AfonsoLopo/migrane-kbd/pcbs/rev3.0/MasterLed.kicad_sch

## KiCad design pcbs/rev3.0/MasterLed.kicad_sch (2025-11-08)

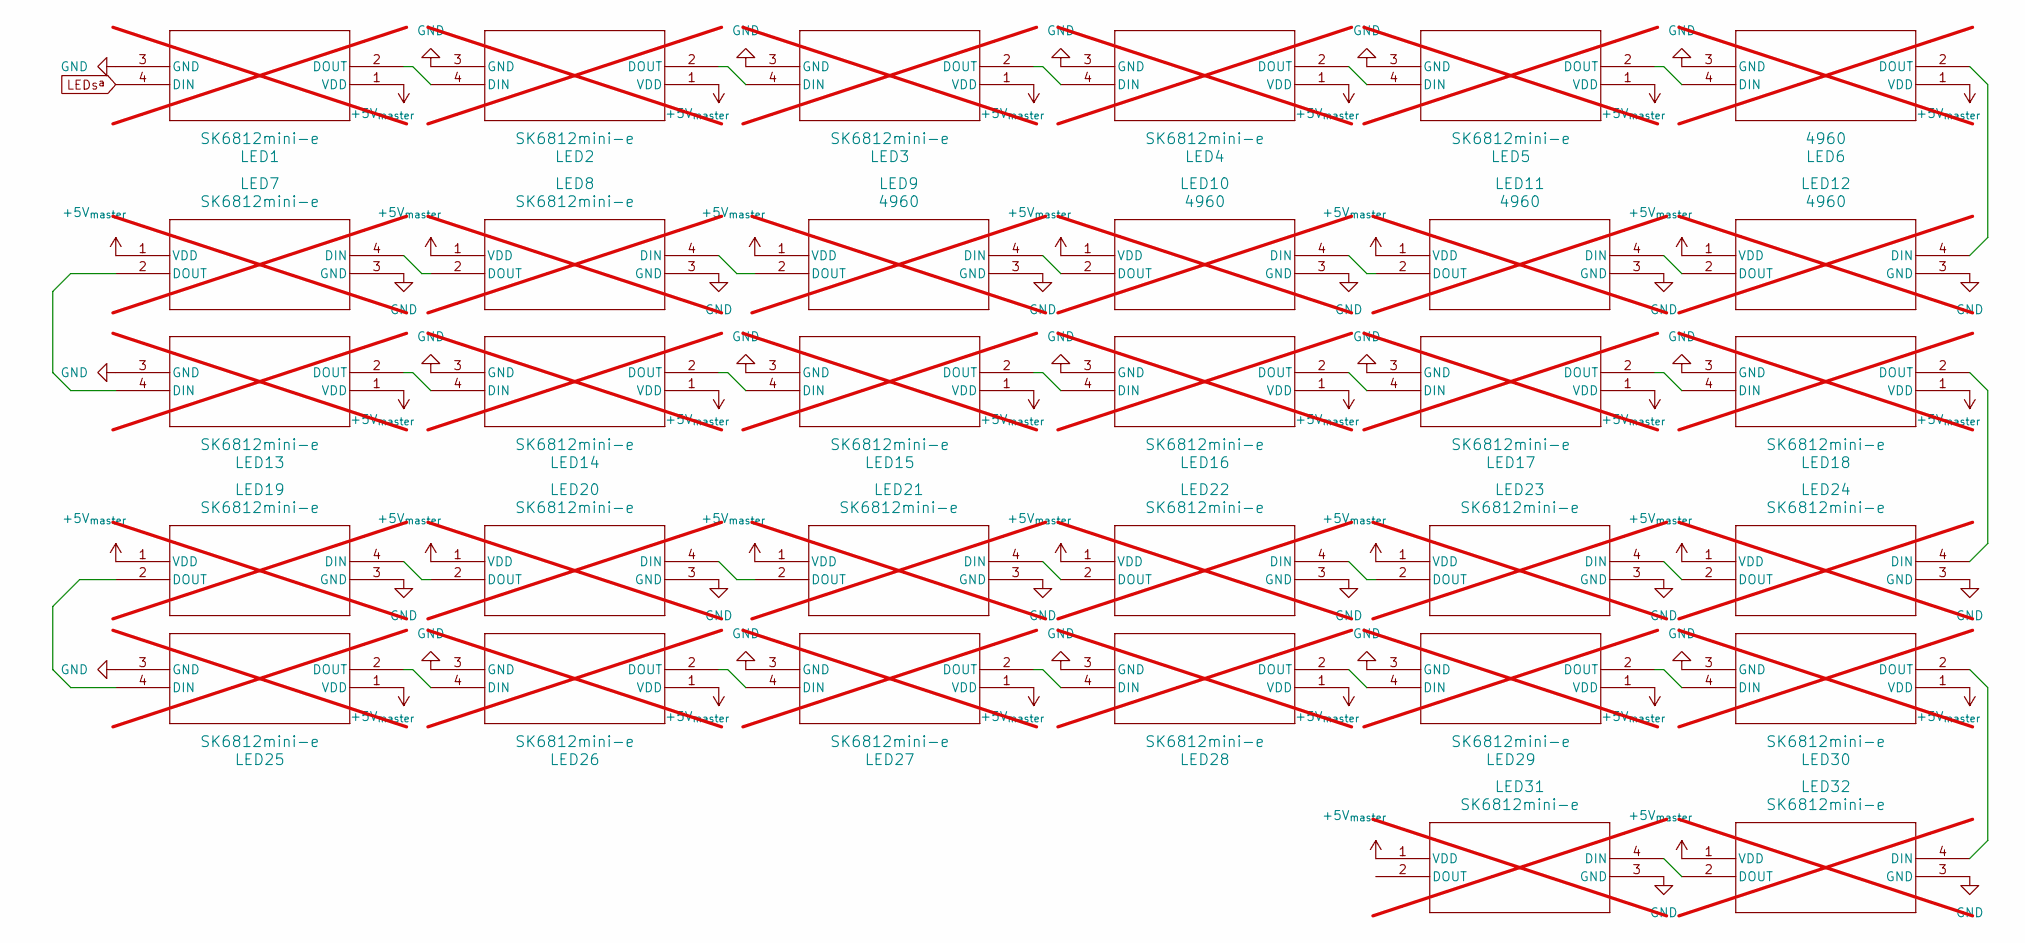
[picture p4: schematic MasterLed.kicad_sch]

Parts:
LED1, LED2, LED3, LED4, LED5, LED7, LED8, LED13, LED14, LED15, LED16, LED17, LED18, LED19, LED20, LED21, LED22, LED23, LED24, LED25, LED26, LED27, LED28, LED29, LED30, LED31, LED32: SK6812mini-e; LED-SMD_L3.2-W2.8-LS5.9_SK6812MINI-E; not fitted
LED6, LED9, LED10, LED11, LED12: 4960; LED-SMD_L3.2-W2.8-LS5.9_SK6812MINI-E; not fitted

Connections:
+5V_{master}: LED1.1 (VDD), LED2.1 (VDD), LED3.1 (VDD), LED4.1 (VDD), LED5.1 (VDD), LED6.1 (VDD), LED7.1 (VDD), LED8.1 (VDD), LED9.1 (VDD), LED10.1 (VDD), LED11.1 (VDD), LED12.1 (VDD), LED13.1 (VDD), LED14.1 (VDD), LED15.1 (VDD), LED16.1 (VDD), LED17.1 (VDD), LED18.1 (VDD), LED19.1 (VDD), LED20.1 (VDD), LED21.1 (VDD), LED22.1 (VDD), LED23.1 (VDD), LED24.1 (VDD), LED25.1 (VDD), LED26.1 (VDD), LED27.1 (VDD), LED28.1 (VDD), LED29.1 (VDD), LED30.1 (VDD), LED31.1 (VDD), LED32.1 (VDD)
GND: LED1.3 (GND), LED2.3 (GND), LED3.3 (GND), LED4.3 (GND), LED5.3 (GND), LED6.3 (GND), LED7.3 (GND), LED8.3 (GND), LED9.3 (GND), LED10.3 (GND), LED11.3 (GND), LED12.3 (GND), LED13.3 (GND), LED14.3 (GND), LED15.3 (GND), LED16.3 (GND), LED17.3 (GND), LED18.3 (GND), LED19.3 (GND), LED20.3 (GND), LED21.3 (GND), LED22.3 (GND), LED23.3 (GND), LED24.3 (GND), LED25.3 (GND), LED26.3 (GND), LED27.3 (GND), LED28.3 (GND), LED29.3 (GND), LED30.3 (GND), LED31.3 (GND), LED32.3 (GND)
LEDs^{a}: LED1.4 (DIN)
unnamed: LED1.2 (DOUT), LED2.4 (DIN)
unnamed: LED2.2 (DOUT), LED3.4 (DIN)
unnamed: LED3.2 (DOUT), LED4.4 (DIN)
unnamed: LED4.2 (DOUT), LED5.4 (DIN)
unnamed: LED5.2 (DOUT), LED6.4 (DIN)
unnamed: LED7.4 (DIN), LED8.2 (DOUT)
unnamed: LED8.4 (DIN), LED9.2 (DOUT)
unnamed: LED9.4 (DIN), LED10.2 (DOUT)
unnamed: LED10.4 (DIN), LED11.2 (DOUT)
unnamed: LED11.4 (DIN), LED12.2 (DOUT)
unnamed: LED6.2 (DOUT), LED12.4 (DIN)
unnamed: LED13.2 (DOUT), LED14.4 (DIN)
unnamed: LED7.2 (DOUT), LED13.4 (DIN)
unnamed: LED14.2 (DOUT), LED15.4 (DIN)
unnamed: LED15.2 (DOUT), LED16.4 (DIN)
unnamed: LED16.2 (DOUT), LED17.4 (DIN)
unnamed: LED17.2 (DOUT), LED18.4 (DIN)
unnamed: LED18.2 (DOUT), LED24.4 (DIN)
unnamed: LED19.2 (DOUT), LED25.4 (DIN)
unnamed: LED19.4 (DIN), LED20.2 (DOUT)
unnamed: LED20.4 (DIN), LED21.2 (DOUT)
unnamed: LED21.4 (DIN), LED22.2 (DOUT)
unnamed: LED22.4 (DIN), LED23.2 (DOUT)
unnamed: LED23.4 (DIN), LED24.2 (DOUT)
unnamed: LED25.2 (DOUT), LED26.4 (DIN)
unnamed: LED26.2 (DOUT), LED27.4 (DIN)
unnamed: LED27.2 (DOUT), LED28.4 (DIN)
unnamed: LED28.2 (DOUT), LED29.4 (DIN)
unnamed: LED29.2 (DOUT), LED30.4 (DIN)
unnamed: LED30.2 (DOUT), LED32.4 (DIN)
unnamed: LED31.4 (DIN), LED32.2 (DOUT)
