AfonsoLopo/migrane-kbd/pcbs/rev3.0/SlaveLed.kicad_sch

## KiCad design pcbs/rev3.0/SlaveLed.kicad_sch (2025-11-08)

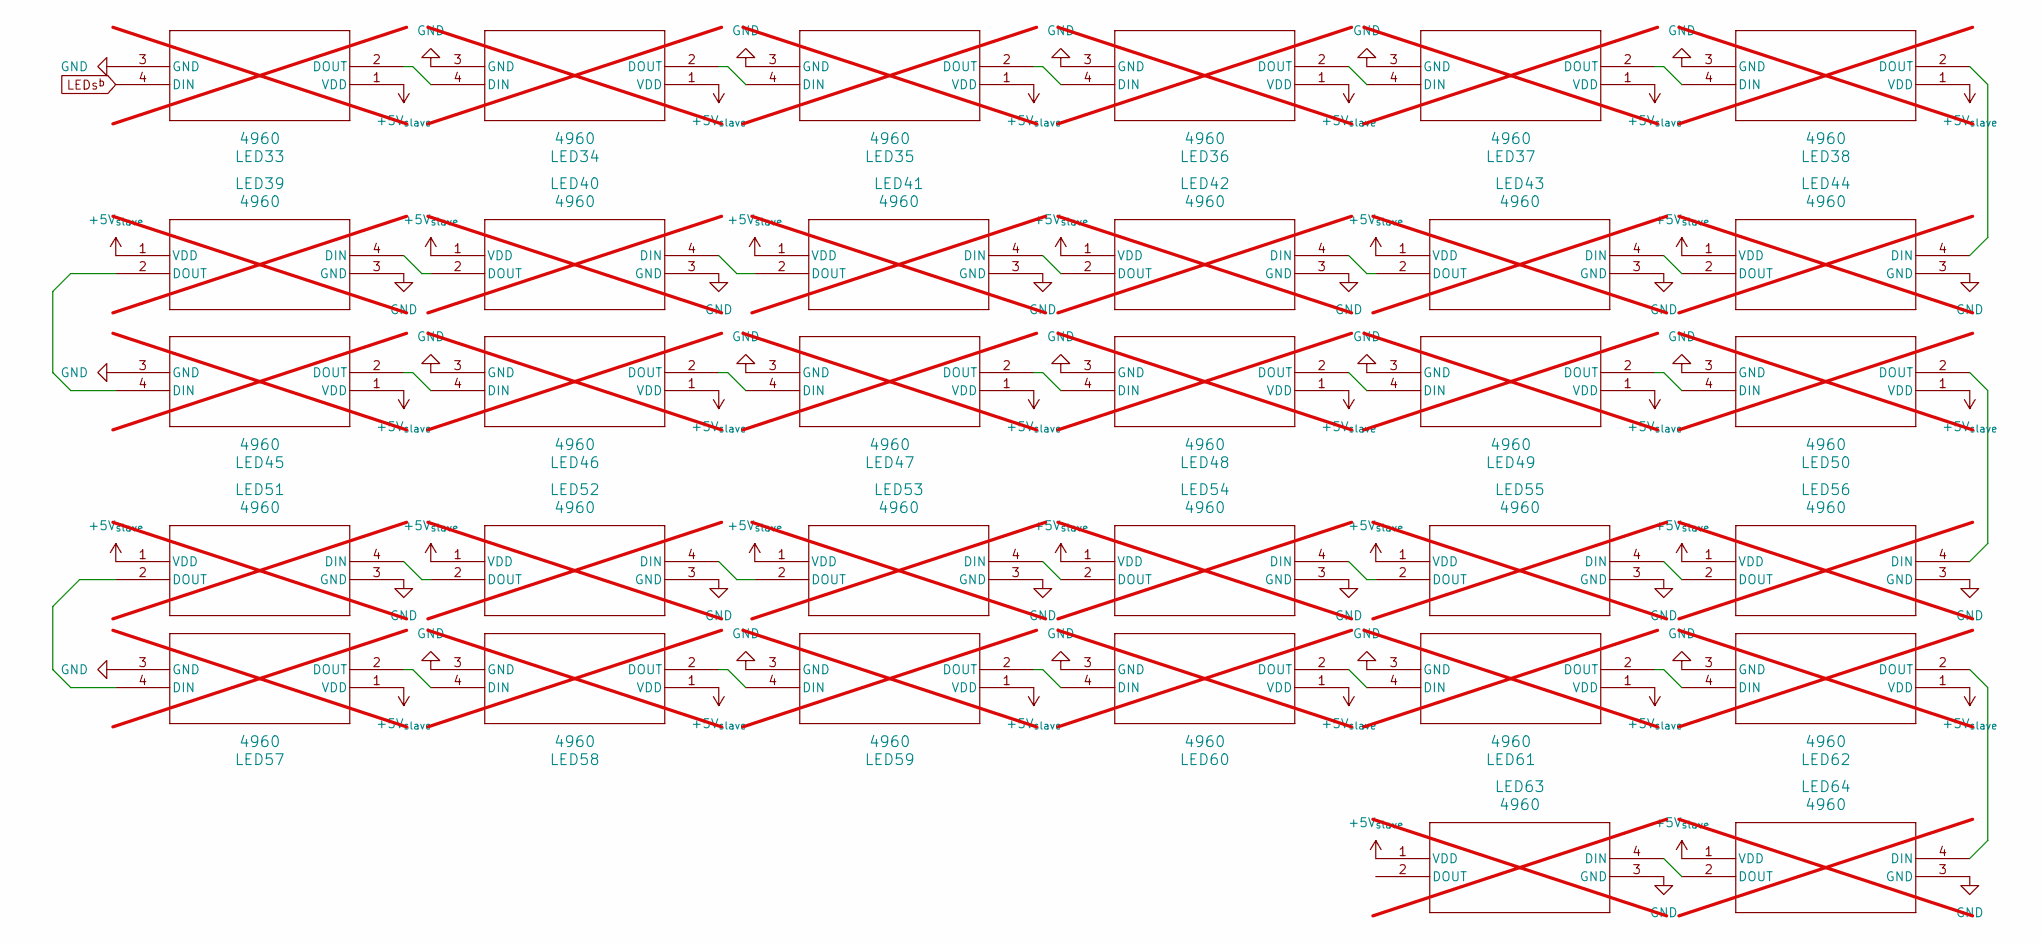
[picture p5: schematic SlaveLed.kicad_sch]

Parts:
LED33, LED34, LED35, LED36, LED37, LED38, LED39, LED40, LED41, LED42, LED43, LED44, LED45, LED46, LED47, LED48, LED49, LED50, LED51, LED52, LED53, LED54, LED55, LED56, LED57, LED58, LED59, LED60, LED61, LED62, LED63, LED64: 4960; LED-SMD_L3.2-W2.8-LS5.9_SK6812MINI-E; not fitted

Connections:
+5V_{slave}: LED33.1 (VDD), LED34.1 (VDD), LED35.1 (VDD), LED36.1 (VDD), LED37.1 (VDD), LED38.1 (VDD), LED39.1 (VDD), LED40.1 (VDD), LED41.1 (VDD), LED42.1 (VDD), LED43.1 (VDD), LED44.1 (VDD), LED45.1 (VDD), LED46.1 (VDD), LED47.1 (VDD), LED48.1 (VDD), LED49.1 (VDD), LED50.1 (VDD), LED51.1 (VDD), LED52.1 (VDD), LED53.1 (VDD), LED54.1 (VDD), LED55.1 (VDD), LED56.1 (VDD), LED57.1 (VDD), LED58.1 (VDD), LED59.1 (VDD), LED60.1 (VDD), LED61.1 (VDD), LED62.1 (VDD), LED63.1 (VDD), LED64.1 (VDD)
GND: LED33.3 (GND), LED34.3 (GND), LED35.3 (GND), LED36.3 (GND), LED37.3 (GND), LED38.3 (GND), LED39.3 (GND), LED40.3 (GND), LED41.3 (GND), LED42.3 (GND), LED43.3 (GND), LED44.3 (GND), LED45.3 (GND), LED46.3 (GND), LED47.3 (GND), LED48.3 (GND), LED49.3 (GND), LED50.3 (GND), LED51.3 (GND), LED52.3 (GND), LED53.3 (GND), LED54.3 (GND), LED55.3 (GND), LED56.3 (GND), LED57.3 (GND), LED58.3 (GND), LED59.3 (GND), LED60.3 (GND), LED61.3 (GND), LED62.3 (GND), LED63.3 (GND), LED64.3 (GND)
LEDs^{b}: LED33.4 (DIN)
unnamed: LED33.2 (DOUT), LED34.4 (DIN)
unnamed: LED34.2 (DOUT), LED35.4 (DIN)
unnamed: LED35.2 (DOUT), LED36.4 (DIN)
unnamed: LED36.2 (DOUT), LED37.4 (DIN)
unnamed: LED37.2 (DOUT), LED38.4 (DIN)
unnamed: LED38.2 (DOUT), LED44.4 (DIN)
unnamed: LED39.2 (DOUT), LED45.4 (DIN)
unnamed: LED39.4 (DIN), LED40.2 (DOUT)
unnamed: LED40.4 (DIN), LED41.2 (DOUT)
unnamed: LED41.4 (DIN), LED42.2 (DOUT)
unnamed: LED42.4 (DIN), LED43.2 (DOUT)
unnamed: LED43.4 (DIN), LED44.2 (DOUT)
unnamed: LED45.2 (DOUT), LED46.4 (DIN)
unnamed: LED46.2 (DOUT), LED47.4 (DIN)
unnamed: LED47.2 (DOUT), LED48.4 (DIN)
unnamed: LED48.2 (DOUT), LED49.4 (DIN)
unnamed: LED49.2 (DOUT), LED50.4 (DIN)
unnamed: LED50.2 (DOUT), LED56.4 (DIN)
unnamed: LED51.2 (DOUT), LED57.4 (DIN)
unnamed: LED51.4 (DIN), LED52.2 (DOUT)
unnamed: LED52.4 (DIN), LED53.2 (DOUT)
unnamed: LED53.4 (DIN), LED54.2 (DOUT)
unnamed: LED54.4 (DIN), LED55.2 (DOUT)
unnamed: LED55.4 (DIN), LED56.2 (DOUT)
unnamed: LED57.2 (DOUT), LED58.4 (DIN)
unnamed: LED58.2 (DOUT), LED59.4 (DIN)
unnamed: LED59.2 (DOUT), LED60.4 (DIN)
unnamed: LED60.2 (DOUT), LED61.4 (DIN)
unnamed: LED61.2 (DOUT), LED62.4 (DIN)
unnamed: LED62.2 (DOUT), LED64.4 (DIN)
unnamed: LED63.4 (DIN), LED64.2 (DOUT)
