AfonsoLopo/migrane-kbd/pcbs/rev3.0/left.kicad_sch

## KiCad design pcbs/rev3.0/left.kicad_sch (2025-11-08)

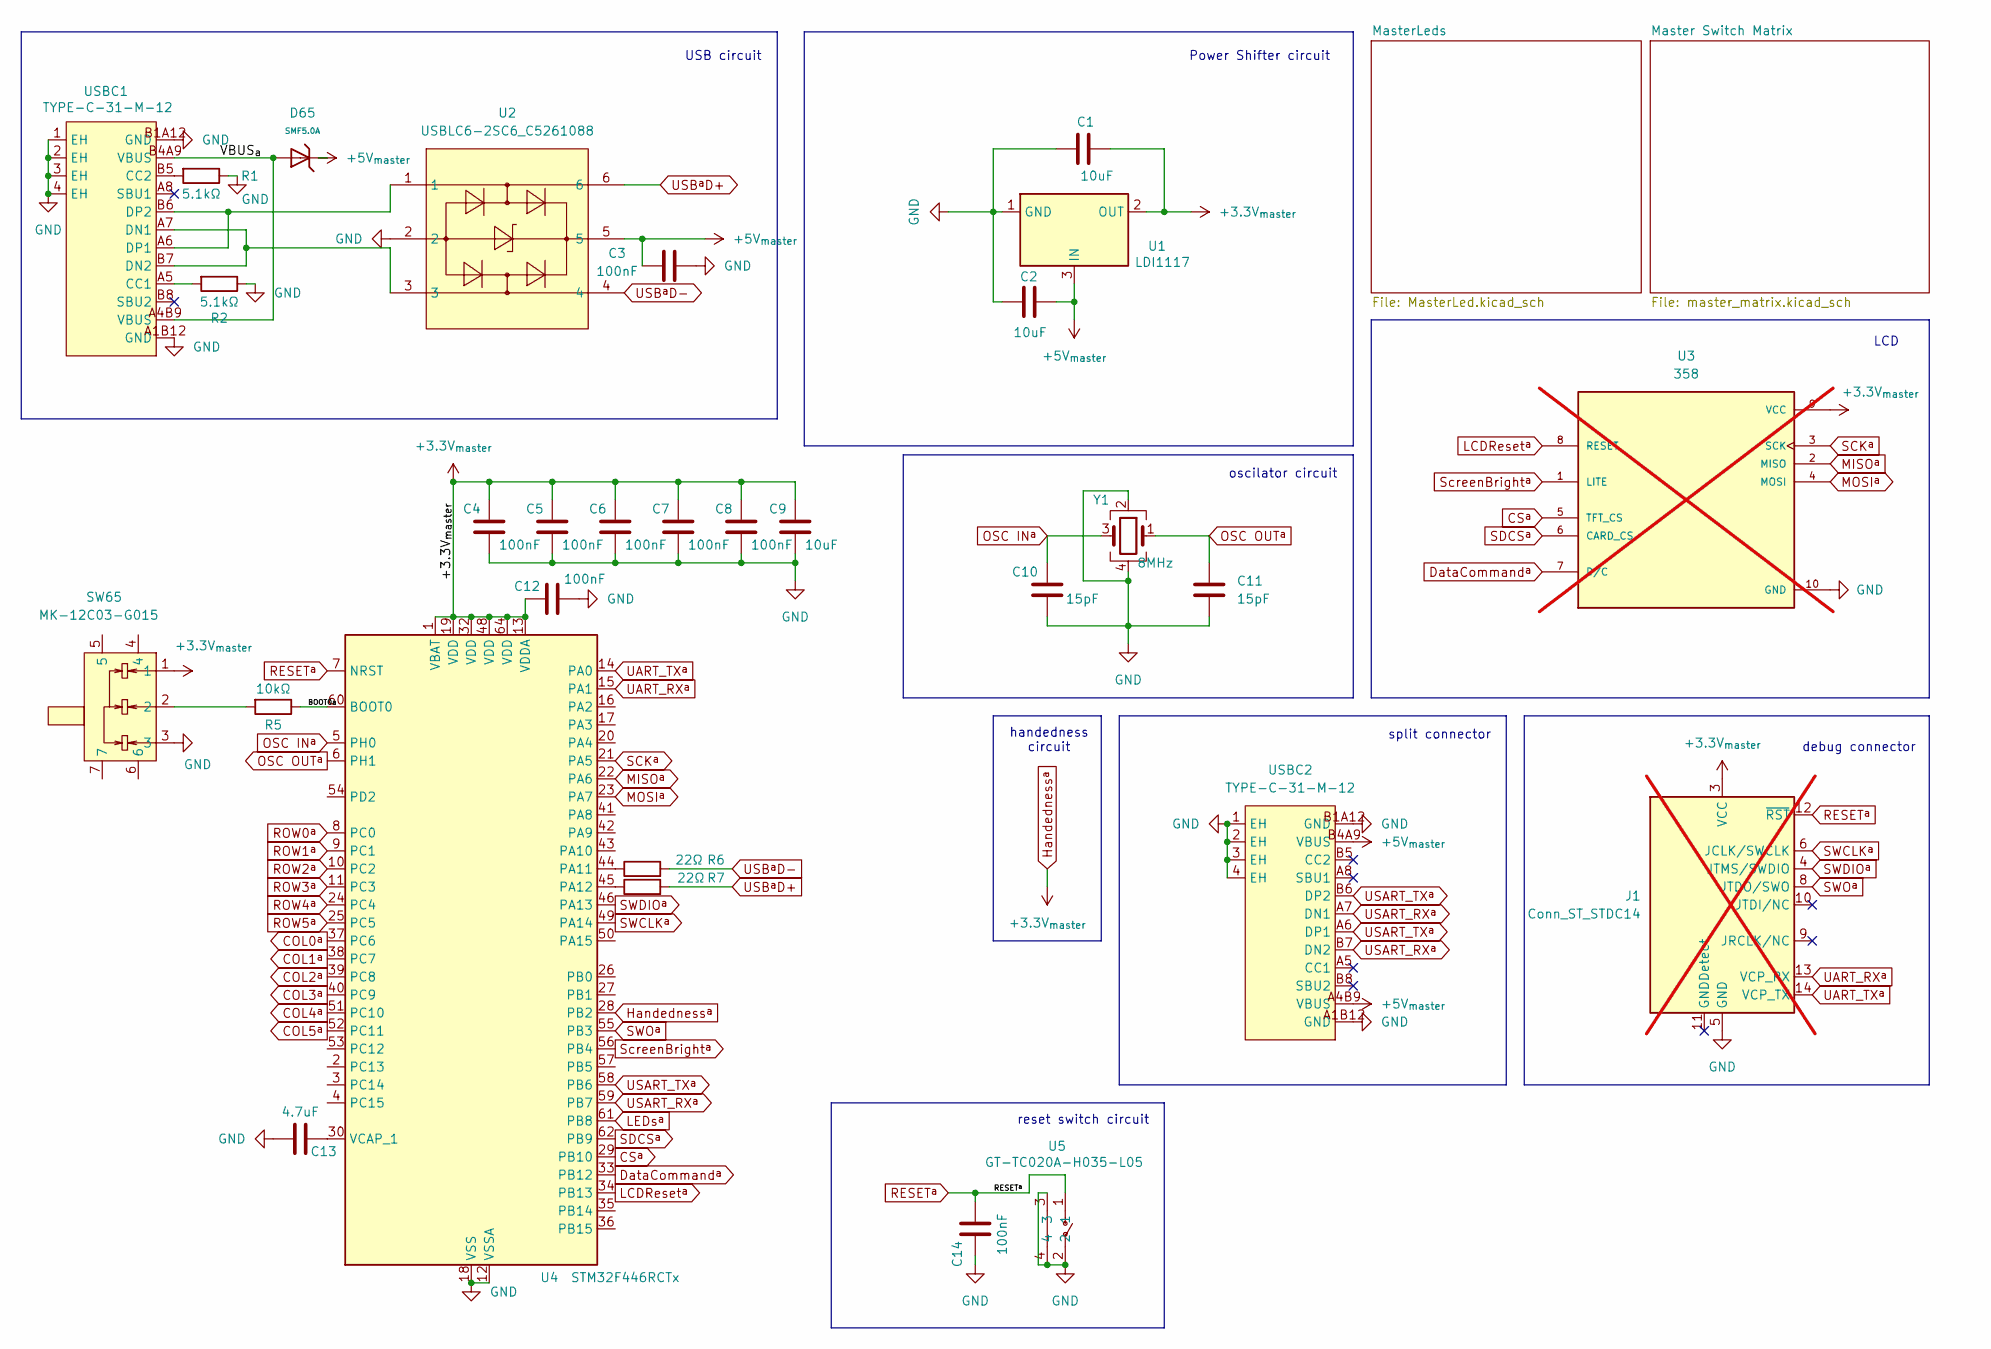
[picture p6: schematic left.kicad_sch]

Parts:
C1, C2, C9: 10uF; C_1206_3216Metric; LCSC C13585
C3, C4, C5, C6, C7, C8, C12, C14: 100nF; C_0805_2012Metric; LCSC C48579599
C10, C11: 15pF; C_0402_1005Metric; LCSC C441742
C13: 4.7uF; C_0603_1608Metric; LCSC C1705
D65: SMF5.0A; D_SOD-123FL; Part SMF5.0A; LCSC C19077497
J1: Conn_ST_STDC14; PinHeader_2x07_P1.27mm_Horizontal; not fitted
R1, R2: 5.1kΩ; R_0603_1608Metric; LCSC C2907114
R5: 10kΩ; R_0805_2012Metric; LCSC C84376
R6, R7: 22Ω; R_0402_1005Metric; LCSC C2906914
SW65: MK-12C03-G015; SW-SMD_MK-12C03-G015; LCSC Part C2890358
U1: LDI1117; SOT-223-3_TabPin2
U2: USBLC6-2SC6_C5261088; SOT-23-6_L2.9-W1.6-P0.95-LS2.8-BR; LCSC Part C5261088
U3: 358; MODULE_358; PARTREV 2021-12-09; not fitted
U4: STM32F446RCTx; LQFP-64_10x10mm_P0.5mm; LCSC C915971
U5: GT-TC020A-H035-L05; SW-SMD_GT-TC020B-H035-L05; LCSC Part C17179533
USBC1, USBC2: TYPE-C-31-M-12; USB-C_SMD-TYPE-C-31-M-12_1; LCSC Part C165948
Y1: 8MHz; Crystal_SMD_Abracon_ABM3B-4Pin_5.0x3.2mm; LCSC C1985378

Connections:
+3.3V_{master}: C1.1, C4.1, C5.1, C6.1, C7.1, C8.1, C9.1, C12.1, J1.3 (VCC), SW65.1, U1.2 (OUT), U3.9 (VCC), U4.1 (VBAT), U4.13 (VDDA), U4.19 (VDD), U4.28 (PB2), U4.32 (VDD), U4.48 (VDD), U4.64 (VDD)
+5V_{master}: C2.2, C3.1, D65.1, U1.3 (IN), U2.5, USBC2.A4B9 (VBUS), USBC2.B4A9 (VBUS)
BOOT0a: R5.1, U4.60 (BOOT0)
COL0^{a}: U4.37 (PC6)
COL1^{a}: U4.38 (PC7)
COL2^{a}: U4.39 (PC8)
COL3^{a}: U4.40 (PC9)
COL4^{a}: U4.51 (PC10)
COL5^{a}: U4.52 (PC11)
CS^{a}: U3.5 (TFT_CS), U4.29 (PB10)
DataCommand^{a}: U3.7 (D/C), U4.33 (PB12)
GND: C1.2, C2.1, C3.2, C4.2, C5.2, C6.2, C7.2, C8.2, C9.2, C10.2, C11.2, C12.2, C13.1, C14.1, J1.5 (GND), J1.7 (GND), R1.1, R2.1, SW65.3, U1.1 (GND), U2.2, U3.10 (GND), U4.12 (VSSA), U4.18 (VSS), U4.31 (VSS), U4.47 (VSS), U4.63 (VSS), U5.2, U5.3, U5.4, USBC1.1 (EH), USBC1.2 (EH), USBC1.3 (EH), USBC1.4 (EH), USBC1.A1B12 (GND), USBC1.B1A12 (GND), USBC2.1 (EH), USBC2.2 (EH), USBC2.3 (EH), USBC2.4 (EH), USBC2.A1B12 (GND), USBC2.B1A12 (GND), Y1.2, Y1.4
LCDReset^{a}: U3.8 (RESET), U4.34 (PB13)
LEDs^{a}: U4.61 (PB8)
MISO^{a}: U3.2 (MISO), U4.22 (PA6)
MOSI^{a}: U3.4 (MOSI), U4.23 (PA7)
unnamed: C13.2, U4.30 (VCAP_1)
unnamed: R1.2, USBC1.B5 (CC2)
unnamed: R2.2, USBC1.A5 (CC1)
unnamed: R5.2, SW65.2
unnamed: R6.1, U4.44 (PA11)
unnamed: R7.1, U4.45 (PA12)
unnamed: U2.1, USBC1.A6 (DP1), USBC1.B6 (DP2)
unnamed: U2.3, USBC1.A7 (DN1), USBC1.B7 (DN2)
OSC IN^{a}: C10.1, U4.5 (PH0), Y1.3
OSC OUT^{a}: C11.1, U4.6 (PH1), Y1.1
RESET^{a}: C14.2, J1.12 (~RST), U4.7 (NRST), U5.1
ROW0^{a}: U4.8 (PC0)
ROW1^{a}: U4.9 (PC1)
ROW2^{a}: U4.10 (PC2)
ROW3^{a}: U4.11 (PC3)
ROW4^{a}: U4.24 (PC4)
ROW5^{a}: U4.25 (PC5)
SCK^{a}: U3.3 (SCK), U4.21 (PA5)
SDCS^{a}: U3.6 (CARD_CS), U4.62 (PB9)
SWCLK^{a}: J1.6 (JCLK/SWCLK), U4.49 (PA14)
SWDIO^{a}: J1.4 (JTMS/SWDIO), U4.46 (PA13)
SWO^{a}: J1.8 (JTDO/SWO), U4.55 (PB3)
ScreenBright^{a}: U3.1 (LITE), U4.56 (PB4)
UART_RX^{a}: J1.13 (VCP_RX), U4.15 (PA1)
UART_TX^{a}: J1.14 (VCP_TX), U4.14 (PA0)
USART_RX^{a}: U4.59 (PB7), USBC2.A7 (DN1), USBC2.B7 (DN2)
USART_TX^{a}: U4.58 (PB6), USBC2.A6 (DP1), USBC2.B6 (DP2)
USB^{a}D+: R7.2, U2.6
USB^{a}D-: R6.2, U2.4
VBUS_{a}: D65.2, USBC1.A4B9 (VBUS), USBC1.B4A9 (VBUS)

Notes on the sheet:
split connector
oscilator circuit
handedness circuit
reset switch circuit
debug connector
USB circuit
Power Shifter circuit
LCD
