AfonsoLopo/migrane-kbd/pcbs/rev3.0/right.kicad_sch

## KiCad design pcbs/rev3.0/right.kicad_sch (2025-11-08)

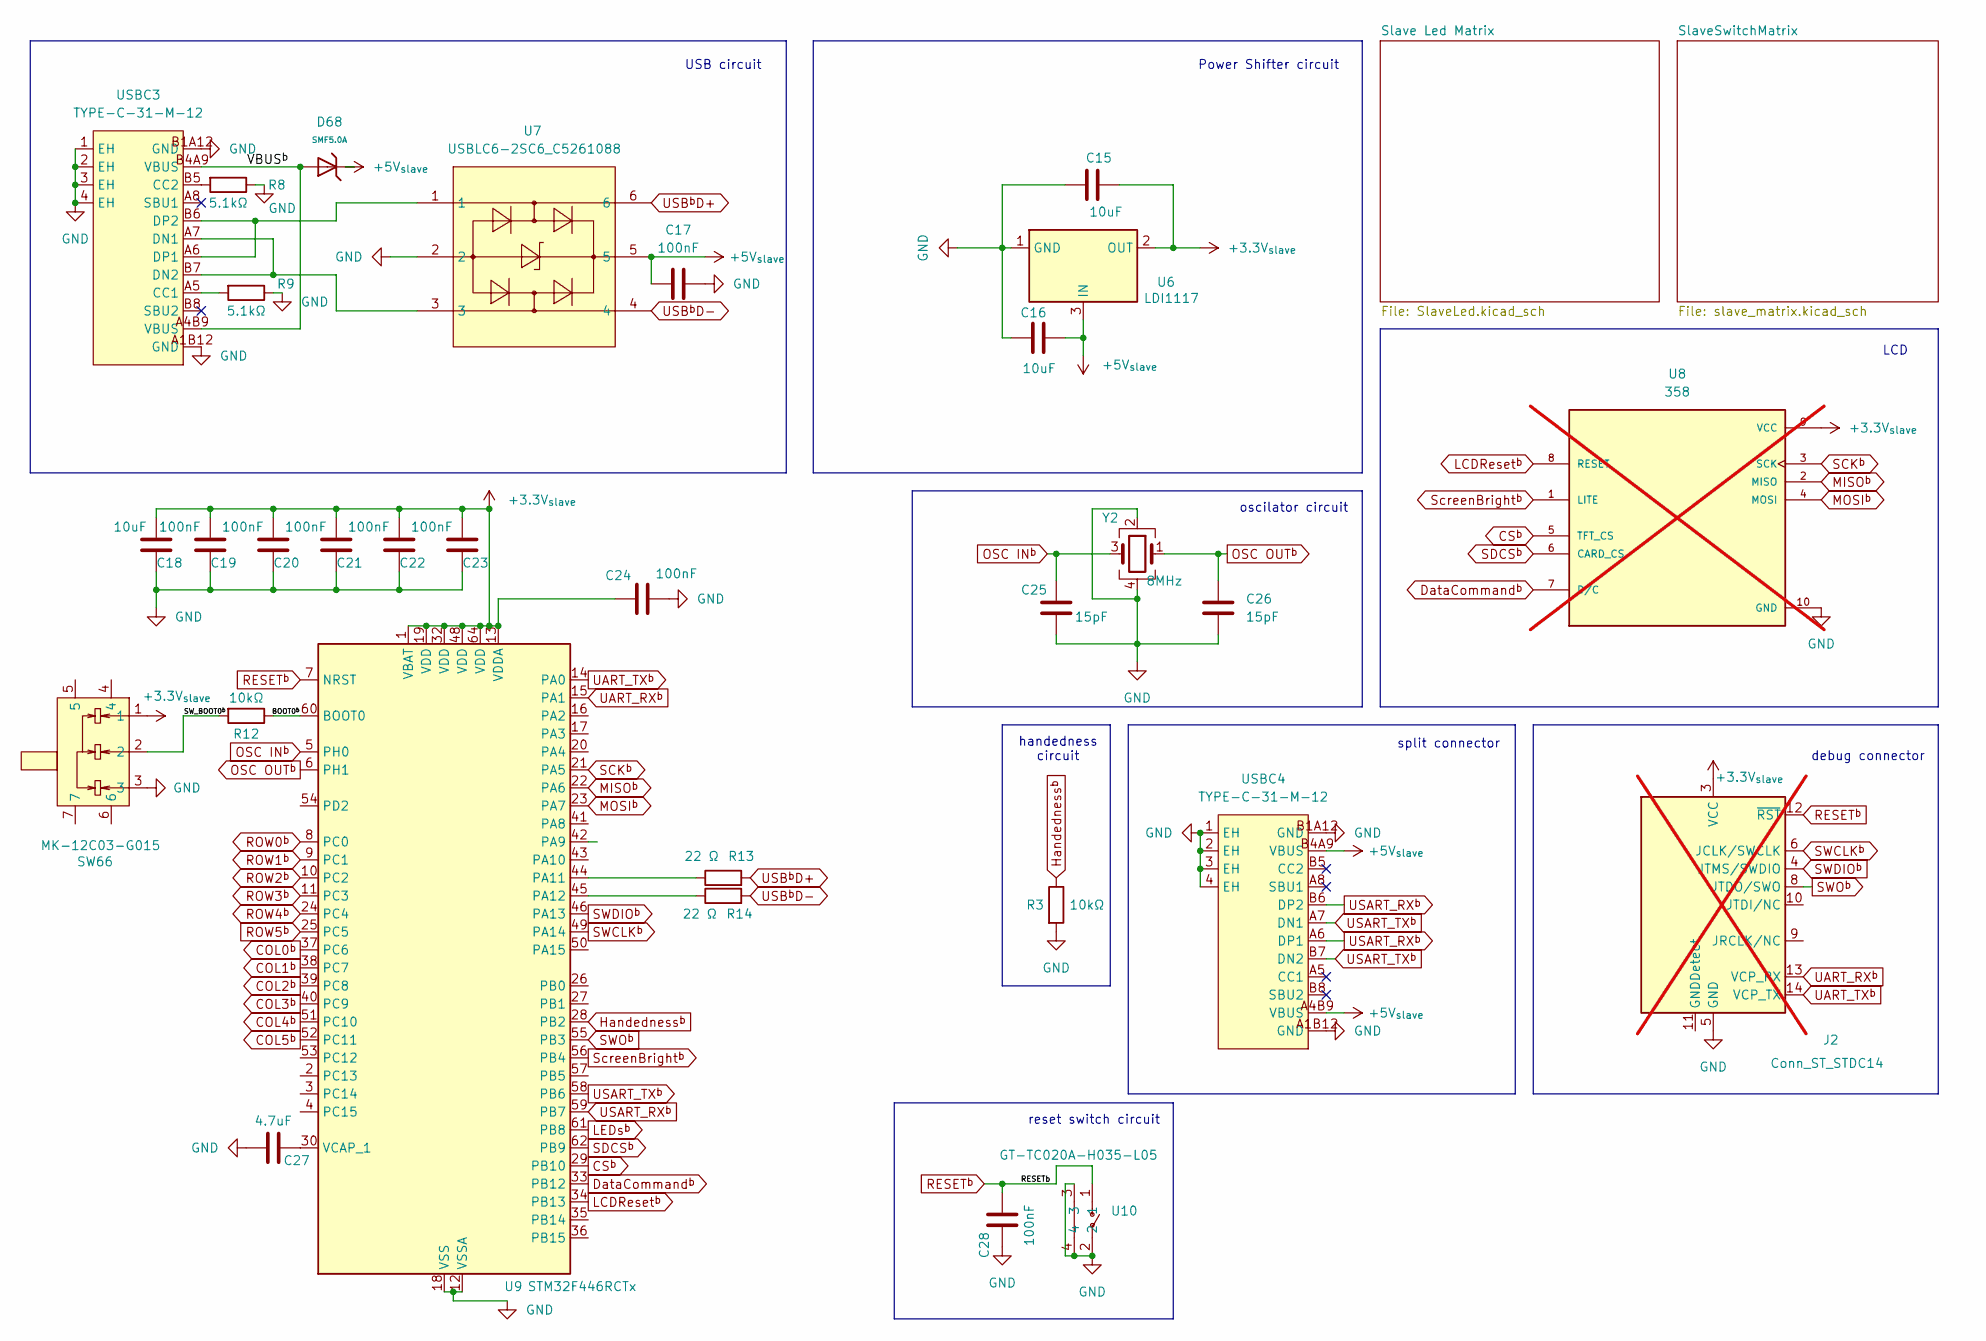
[picture p8: schematic right.kicad_sch]

Parts:
C15, C16, C18: 10uF; C_1206_3216Metric; LCSC C13585
C17, C19, C20, C21, C22, C23, C24, C28: 100nF; C_0805_2012Metric; LCSC C48579599
C25, C26: 15pF; C_0402_1005Metric; LCSC C441742
C27: 4.7uF; C_0603_1608Metric; LCSC C1705
D68: SMF5.0A; D_SOD-123FL; Part SMF5.0A; LCSC C19077497
J2: Conn_ST_STDC14; PinHeader_2x07_P1.27mm_Horizontal; not fitted
R3: 10kΩ; R_0805_2012Metric
R8, R9: 5.1kΩ; R_0603_1608Metric; LCSC C2907114
R12: 10kΩ; R_0805_2012Metric; LCSC C84376
R13, R14: 22 Ω; R_0402_1005Metric; LCSC C2906914
SW66: MK-12C03-G015; SW-SMD_MK-12C03-G015; LCSC Part C2890358
U6: LDI1117; SOT-223-3_TabPin2
U7: USBLC6-2SC6_C5261088; SOT-23-6_L2.9-W1.6-P0.95-LS2.8-BR; LCSC Part C5261088
U8: 358; MODULE_358; PARTREV 2021-12-09; not fitted
U9: STM32F446RCTx; LQFP-64_10x10mm_P0.5mm; LCSC C915971
U10: GT-TC020A-H035-L05; SW-SMD_GT-TC020B-H035-L05; LCSC Part C17179533
USBC3, USBC4: TYPE-C-31-M-12; USB-C_SMD-TYPE-C-31-M-12_1; LCSC Part C165948
Y2: 8MHz; Crystal_SMD_Abracon_ABM3B-4Pin_5.0x3.2mm; LCSC C1985378

Connections:
+3.3V_{slave}: C15.1, C18.2, C19.2, C20.2, C21.2, C22.2, C23.2, C24.2, J2.3 (VCC), SW66.1, U6.2 (OUT), U8.9 (VCC), U9.1 (VBAT), U9.13 (VDDA), U9.19 (VDD), U9.32 (VDD), U9.48 (VDD), U9.64 (VDD)
+5V_{slave}: C16.2, C17.1, D68.1, U6.3 (IN), U7.5, USBC4.A4B9 (VBUS), USBC4.B4A9 (VBUS)
BOOT0^{b}: R12.1, U9.60 (BOOT0)
COL0^{b}: U9.37 (PC6)
COL1^{b}: U9.38 (PC7)
COL2^{b}: U9.39 (PC8)
COL3^{b}: U9.40 (PC9)
COL4^{b}: U9.51 (PC10)
COL5^{b}: U9.52 (PC11)
CS^{b}: U8.5 (TFT_CS), U9.29 (PB10)
DataCommand^{b}: U8.7 (D/C), U9.33 (PB12)
GND: C15.2, C16.1, C17.2, C18.1, C19.1, C20.1, C21.1, C22.1, C23.1, C24.1, C25.2, C26.2, C27.1, C28.1, J2.5 (GND), J2.7 (GND), R3.2, R8.1, R9.1, SW66.3, U6.1 (GND), U7.2, U8.10 (GND), U9.12 (VSSA), U9.18 (VSS), U9.31 (VSS), U9.47 (VSS), U9.63 (VSS), U10.2, U10.3, U10.4, USBC3.1 (EH), USBC3.2 (EH), USBC3.3 (EH), USBC3.4 (EH), USBC3.A1B12 (GND), USBC3.B1A12 (GND), USBC4.1 (EH), USBC4.2 (EH), USBC4.3 (EH), USBC4.4 (EH), USBC4.A1B12 (GND), USBC4.B1A12 (GND), Y2.2, Y2.4
Handedness^{b}: R3.1, U9.28 (PB2)
LCDReset^{b}: U8.8 (RESET), U9.34 (PB13)
LEDs^{b}: U9.61 (PB8)
MISO^{b}: U8.2 (MISO), U9.22 (PA6)
MOSI^{b}: U8.4 (MOSI), U9.23 (PA7)
unnamed: C27.2, U9.30 (VCAP_1)
unnamed: R8.2, USBC3.B5 (CC2)
unnamed: R9.2, USBC3.A5 (CC1)
unnamed: R13.1, U9.44 (PA11)
unnamed: R14.1, U9.45 (PA12)
unnamed: U7.1, USBC3.A6 (DP1), USBC3.B6 (DP2)
unnamed: U7.3, USBC3.A7 (DN1), USBC3.B7 (DN2)
OSC IN^{b}: C25.1, U9.5 (PH0), Y2.3
OSC OUT^{b}: C26.1, U9.6 (PH1), Y2.1
RESET^{b}: C28.2, J2.12 (~RST), U9.7 (NRST), U10.1
ROW0^{b}: U9.8 (PC0)
ROW1^{b}: U9.9 (PC1)
ROW2^{b}: U9.10 (PC2)
ROW3^{b}: U9.11 (PC3)
ROW4^{b}: U9.24 (PC4)
ROW5^{b}: U9.25 (PC5)
SCK^{b}: U8.3 (SCK), U9.21 (PA5)
SDCS^{b}: U8.6 (CARD_CS), U9.62 (PB9)
SWCLK^{b}: J2.6 (JCLK/SWCLK), U9.49 (PA14)
SWDIO^{b}: J2.4 (JTMS/SWDIO), U9.46 (PA13)
SWO^{b}: J2.8 (JTDO/SWO), U9.55 (PB3)
SW_BOOT0^{b}: R12.2, SW66.2
ScreenBright^{b}: U8.1 (LITE), U9.56 (PB4)
UART_RX^{b}: J2.13 (VCP_RX), U9.15 (PA1)
UART_TX^{b}: J2.14 (VCP_TX), U9.14 (PA0)
USART_RX^{b}: U9.59 (PB7), USBC4.A6 (DP1), USBC4.B6 (DP2)
USART_TX^{b}: U9.58 (PB6), USBC4.A7 (DN1), USBC4.B7 (DN2)
USB^{b}D+: R13.2, U7.6
USB^{b}D-: R14.2, U7.4
VBUS^{b}: D68.2, USBC3.A4B9 (VBUS), USBC3.B4A9 (VBUS)

Notes on the sheet:
reset switch circuit
split connector
debug connector
Power Shifter circuit
handedness circuit
oscilator circuit
USB circuit
LCD
