AfonsoLopo/migrane-kbd/pcbs/rev3.0/slave_matrix.kicad_sch

## KiCad design pcbs/rev3.0/slave_matrix.kicad_sch (2025-11-08)

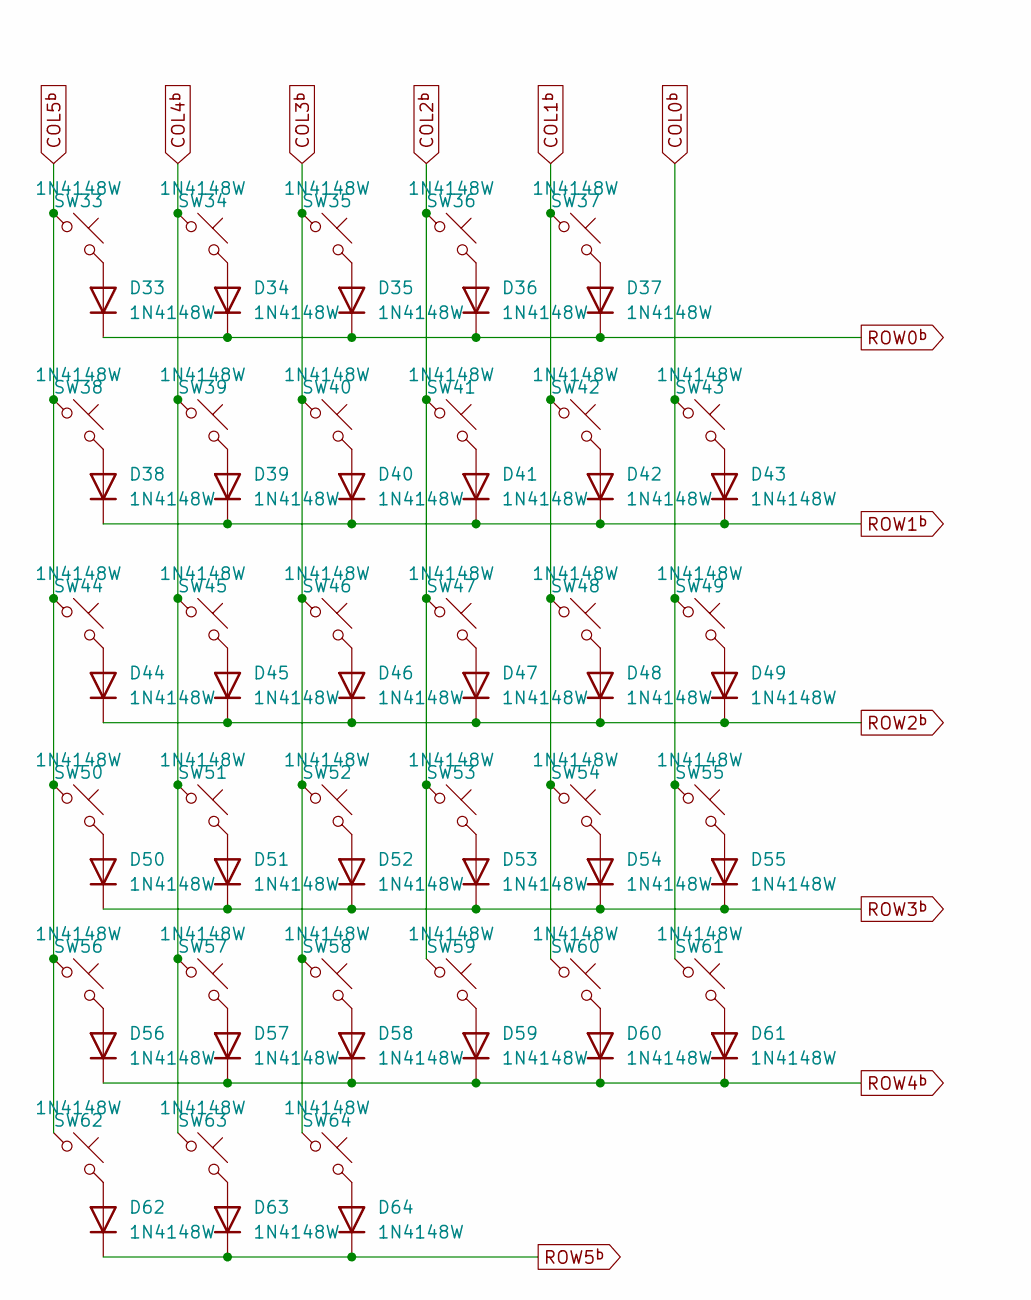
[picture p9: schematic slave_matrix.kicad_sch]

Parts:
D33, D34, D35, D36, D37, D38, D39, D40, D41, D42, D43, D44, D45, D46, D47, D48, D49, D50, D51, D52, D53, D54, D55, D56, D57, D58, D59, D60, D61, D62, D63, D64: 1N4148W; D_SOD-123; LCSC C917030
SW33, SW34, SW35, SW36, SW37, SW38, SW39, SW40, SW41, SW42, SW43, SW44, SW45, SW46, SW47, SW48, SW49, SW50, SW51, SW52, SW53, SW54, SW55, SW56, SW57, SW58, SW59, SW60, SW61, SW63, SW64: 1N4148W; SW_Hotswap_Kailh_Choc_V1_Plated_1.00u; LCSC C917030
SW62: 1N4148W; SW_Hotswap_Kailh_Choc_V1_Plated_1.50u; LCSC C917030

Connections:
COL0^{b}: SW43.1, SW49.1, SW55.1, SW61.1
COL1^{b}: SW37.1, SW42.1, SW48.1, SW54.1, SW60.1
COL2^{b}: SW36.1, SW41.1, SW47.1, SW53.1, SW59.1
COL3^{b}: SW35.1, SW40.1, SW46.1, SW52.1, SW58.1, SW64.1
COL4^{b}: SW34.1, SW39.1, SW45.1, SW51.1, SW57.1, SW63.1
COL5^{b}: SW33.1, SW38.1, SW44.1, SW50.1, SW56.1, SW62.1
unnamed: D33.2 (A), SW33.2
unnamed: D34.2 (A), SW34.2
unnamed: D35.2 (A), SW35.2
unnamed: D36.2 (A), SW36.2
unnamed: D37.2 (A), SW37.2
unnamed: D38.2 (A), SW38.2
unnamed: D39.2 (A), SW39.2
unnamed: D40.2 (A), SW40.2
unnamed: D41.2 (A), SW41.2
unnamed: D42.2 (A), SW42.2
unnamed: D43.2 (A), SW43.2
unnamed: D44.2 (A), SW44.2
unnamed: D45.2 (A), SW45.2
unnamed: D46.2 (A), SW46.2
unnamed: D47.2 (A), SW47.2
unnamed: D48.2 (A), SW48.2
unnamed: D49.2 (A), SW49.2
unnamed: D50.2 (A), SW50.2
unnamed: D51.2 (A), SW51.2
unnamed: D52.2 (A), SW52.2
unnamed: D53.2 (A), SW53.2
unnamed: D54.2 (A), SW54.2
unnamed: D55.2 (A), SW55.2
unnamed: D56.2 (A), SW56.2
unnamed: D57.2 (A), SW57.2
unnamed: D58.2 (A), SW58.2
unnamed: D59.2 (A), SW59.2
unnamed: D60.2 (A), SW60.2
unnamed: D61.2 (A), SW61.2
unnamed: D62.2 (A), SW62.2
unnamed: D63.2 (A), SW63.2
unnamed: D64.2 (A), SW64.2
ROW0^{b}: D33.1 (K), D34.1 (K), D35.1 (K), D36.1 (K), D37.1 (K)
ROW1^{b}: D38.1 (K), D39.1 (K), D40.1 (K), D41.1 (K), D42.1 (K), D43.1 (K)
ROW2^{b}: D44.1 (K), D45.1 (K), D46.1 (K), D47.1 (K), D48.1 (K), D49.1 (K)
ROW3^{b}: D50.1 (K), D51.1 (K), D52.1 (K), D53.1 (K), D54.1 (K), D55.1 (K)
ROW4^{b}: D56.1 (K), D57.1 (K), D58.1 (K), D59.1 (K), D60.1 (K), D61.1 (K)
ROW5^{b}: D62.1 (K), D63.1 (K), D64.1 (K)
